JasonFischell/FischellFancyFlashLight/Software/Milestone 3/Software Flowchart PDF.pdf

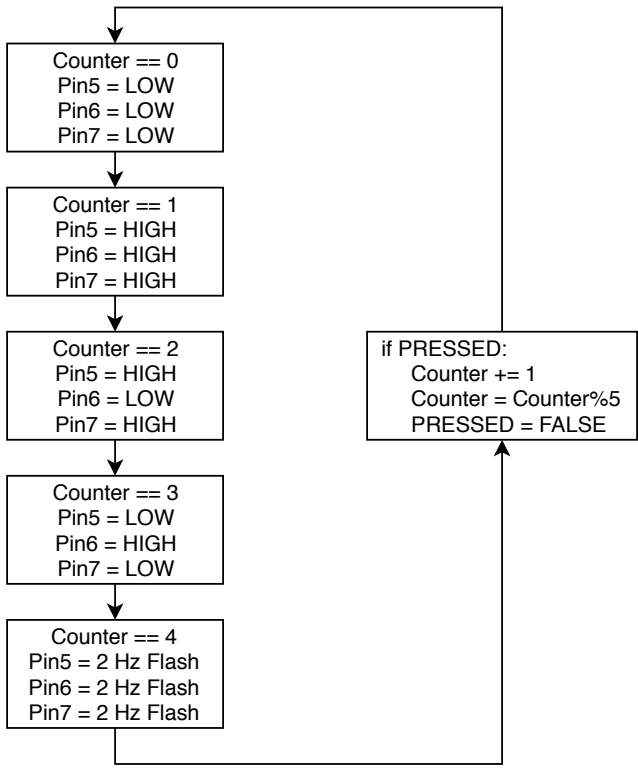
[picture p7: figure]
Counter == 0 Pin5 = LOW Pin6 = LOW Pin7 = LOW; Counter == 1 Pin5 = HIGH Pin6 = HIGH Pin7 = HIGH; Counter == 2 Pin5 = HIGH Pin6 = LOW Pin7 = HIGH; Counter == 3 Pin5 = LOW Pin6 = HIGH Pin7 = LOW; Counter == 4 Pin5 = 2 Hz Flash Pin6 = 2 Hz Flash Pin7 = 2 Hz Flash; if PRESSED: Counter += 1 Counter = Counter%5 PRESSED = FALSE

Pin 4 Rising Edge
Interrupt -
PRESSED = TRUE

# INTERRUPT
