JasonFischell/FischellFancyFlashLight/Mechanical/Milestone 5/Failed Assembly.SLDASM

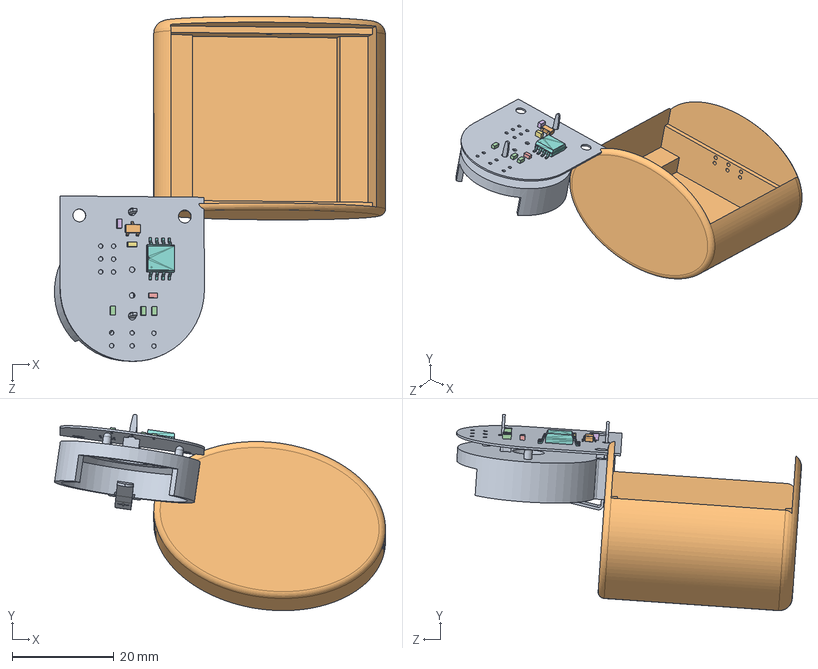
[picture p15: CAD file, 2018-11-19]
Mechanical/Milestone 5/Failed Assembly.SLDASM
64.9 x 38.5 x 67.7 mm
Board
SOT23-3
Extruded
Extruded_2 x 3
Extruded_3
Extruded_4
Extruded_5
8S2
keystone-PN1025-7
Bottom
