JasonFischell/FischellFancyFlashLight/Mechanical/Milestone 5/Final Case Bottom.SLDPRT

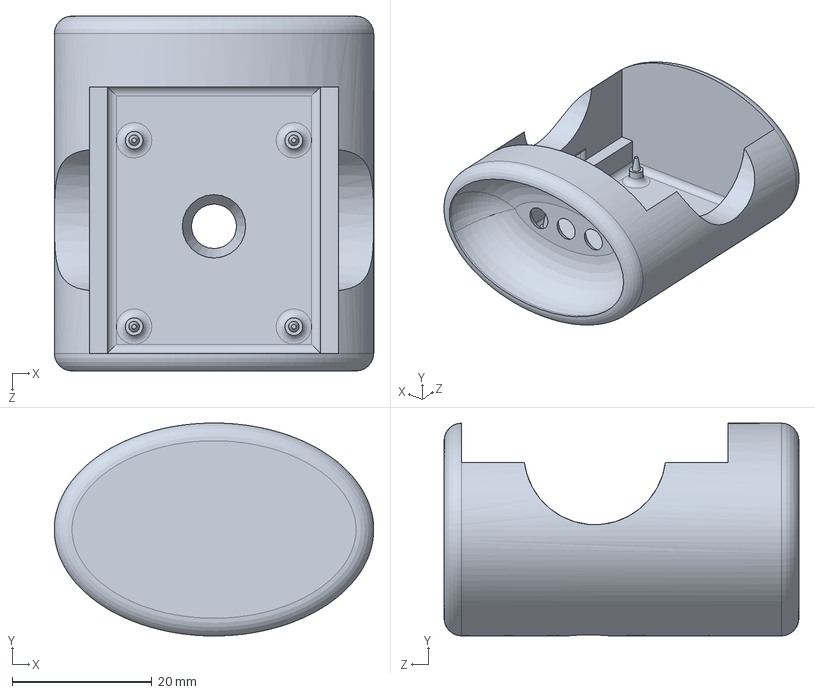
[picture p16: CAD file, 2018-12-10]
Mechanical/Milestone 5/Final Case Bottom.SLDPRT
45.7 x 30.5 x 50.8 mm
