JasonFischell/FischellFancyFlashLight/Mechanical/Milestone 5/Final Case Top.SLDPRT

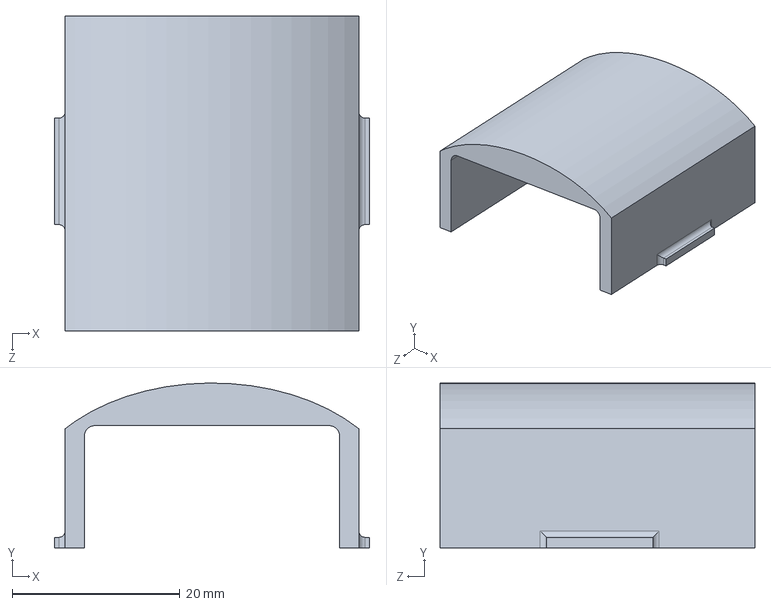
[picture p17: CAD file, 2018-12-10]
Mechanical/Milestone 5/Final Case Top.SLDPRT
37.6 x 19.7 x 37.6 mm
