JasonFischell/FischellFancyFlashLight/Mechanical/Milestone 5/Thick Clip Bottom.STL

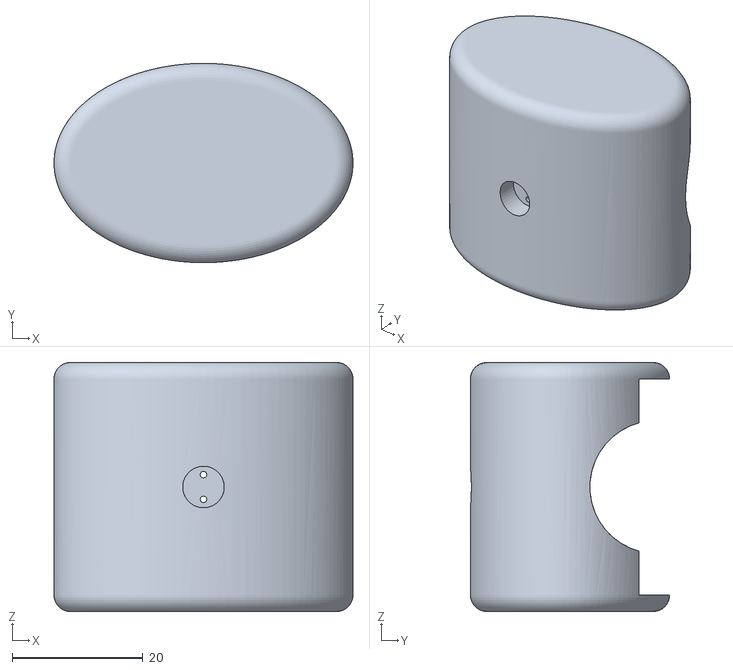
[picture p18: CAD file, 2018-12-10]
Mechanical/Milestone 5/Thick Clip Bottom.STL
45.7 x 30.5 x 38.1
