JasonFischell/FischellFancyFlashLight/Mechanical/Milestone 5/Final Flashlight PCB.step

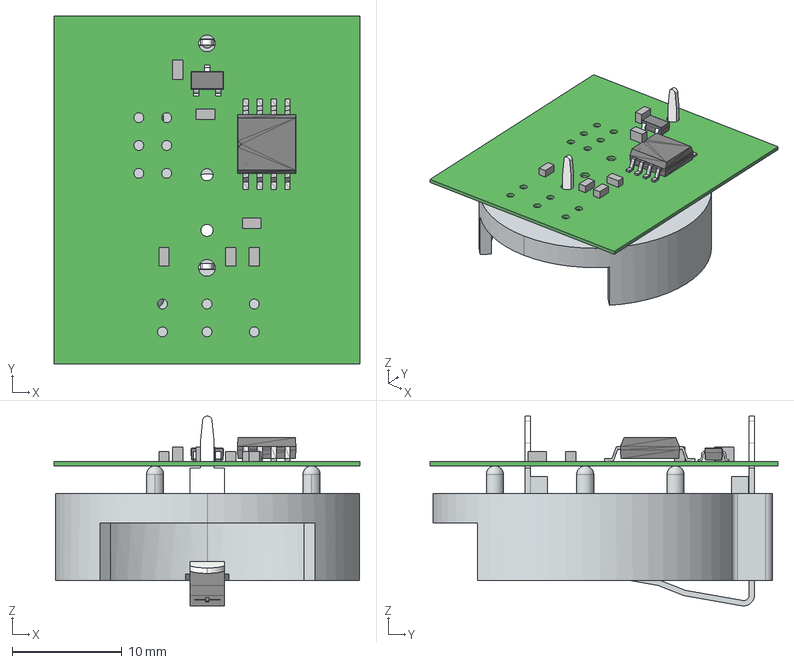
[picture p19: CAD file, 2018-11-28]
Mechanical/Milestone 5/Final Flashlight PCB.step
27.9 x 31.8 x 17.3 mm
Board
keystone-PN1025-7
SOT23-3
Extruded x 7
8S2
