JasonFischell/FischellFancyFlashLight/Mechanical/Milestone 5/Clip Top.SLDPRT

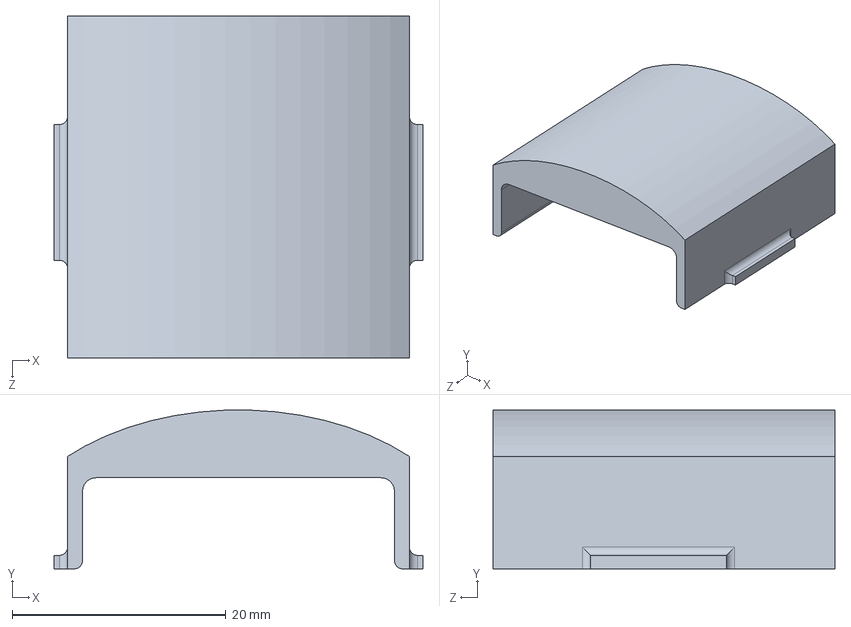
[picture p20: CAD file, 2018-11-26]
Mechanical/Milestone 5/Clip Top.SLDPRT
34.5 x 14.9 x 32.0 mm
