JasonFischell/FischellFancyFlashLight/Mechanical/Milestone 5/Bottom.SLDPRT

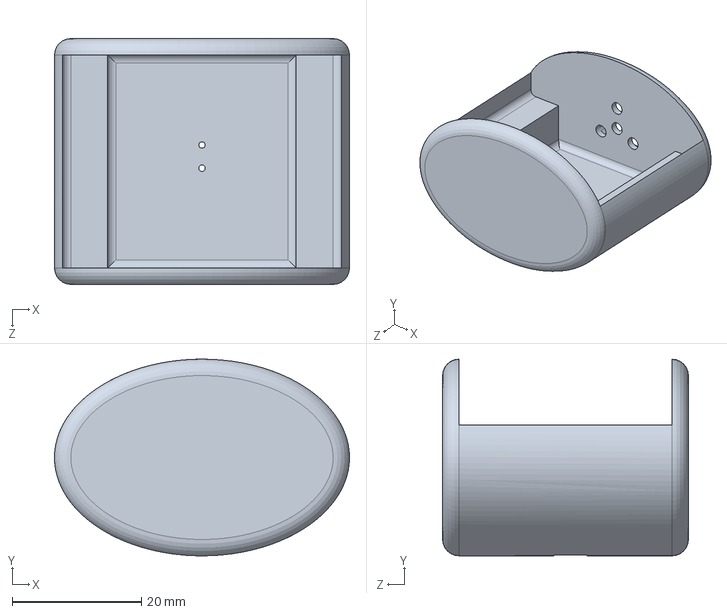
[picture p21: CAD file, 2018-11-26]
Mechanical/Milestone 5/Bottom.SLDPRT
45.7 x 30.5 x 38.1 mm
