JasonFischell/FischellFancyFlashLight/Mechanical/Milestone 5/Velcro Top.SLDPRT

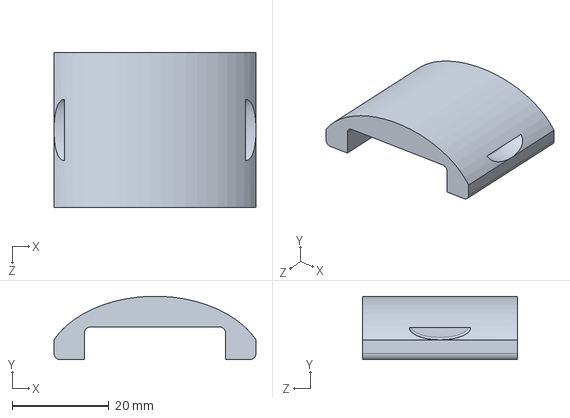
[picture p22: CAD file, 2018-11-26]
Mechanical/Milestone 5/Velcro Top.SLDPRT
41.7 x 13.1 x 32.0 mm
