JasonFischell/FischellFancyFlashLight/Mechanical/Milestone 5/Flashlight PCB 2.step

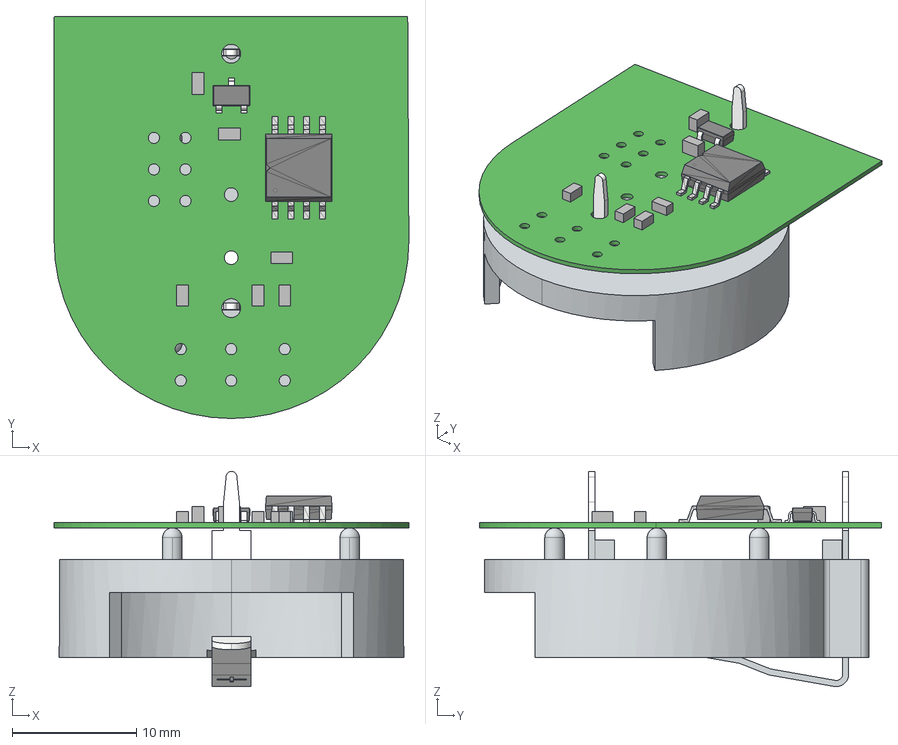
[picture p23: CAD file, 2018-11-19]
Mechanical/Milestone 5/Flashlight PCB 2.step
28.6 x 32.4 x 17.3 mm
Board
SOT23-3
Extruded x 7
8S2
keystone-PN1025-7
