JasonFischell/FischellFancyFlashLight/Mechanical/Milestone 5/Part9.SLDPRT

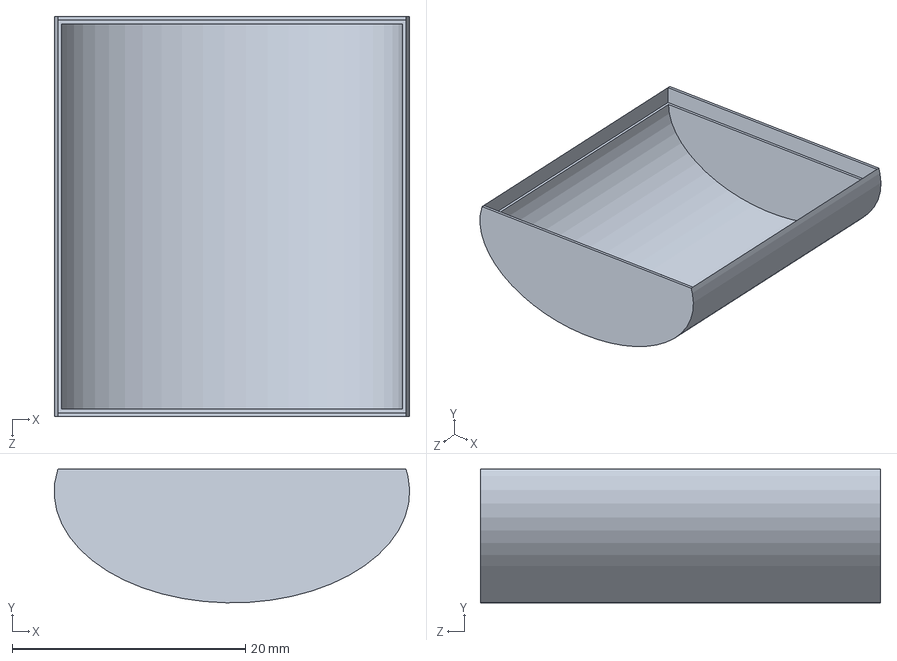
[picture p24: CAD file, 2018-11-19]
Mechanical/Milestone 5/Part9.SLDPRT
30.5 x 11.5 x 34.3 mm
