JasonFischell/FischellFancyFlashLight/Testing/Hardware Testing/20181126_164756.jpg

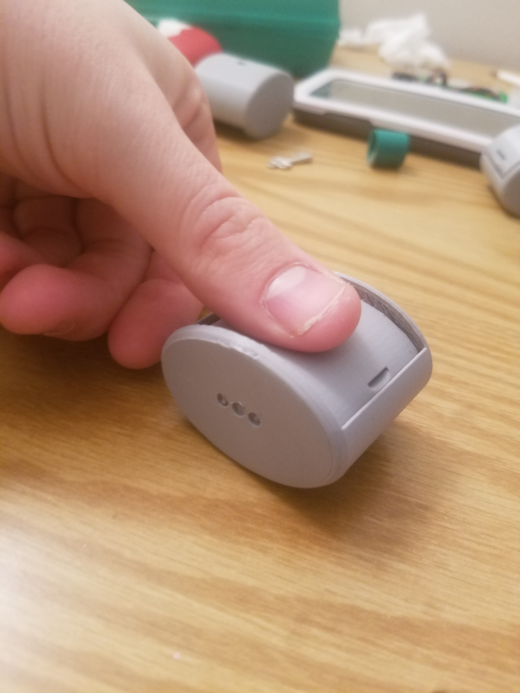
Testing/Hardware Testing/20181126_164756.jpg
