JasonFischell/FischellFancyFlashLight/Testing/Hardware Testing/20181126_164909.jpg

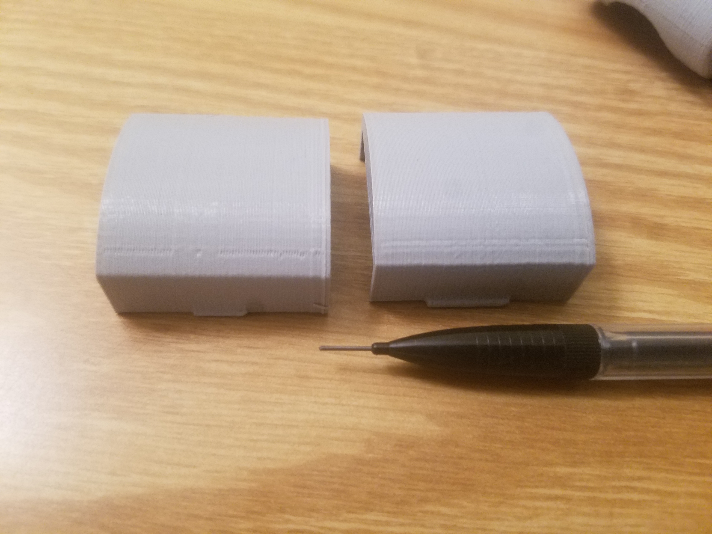
Testing/Hardware Testing/20181126_164909.jpg
