JasonFischell/FischellFancyFlashLight/Testing/Hardware Testing/20181126_164928.jpg

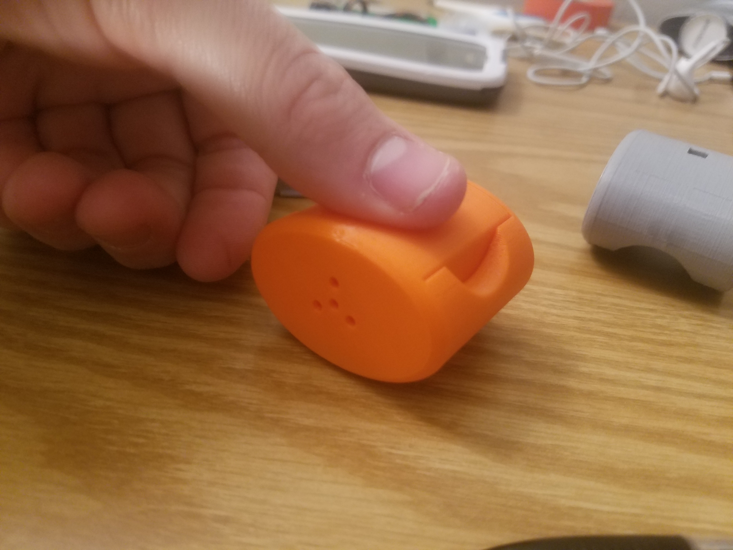
Testing/Hardware Testing/20181126_164928.jpg
